SloBloLabs/LivSynth/App/System/Clock.cpp

#include "Clock.h"
#include "main.h"
#include "Groove.h"
#include <cmath>
#include "MidiMessage.h"
#include "swvPrint.h"
#include "System.h"

Clock::Clock(ClockTimer &timer) :
    _timer(timer)
{
    resetTicks();
    _ppqn = CONFIG_PPQN;
    _masterBpm = 120.f;
    _runState = RunState::Idle;
    _slaveDivisor = CONFIG_PPQN / 24; // -> 8
    _timer.attach(this);
}

void Clock::init() {
    _timer.disable();
}

void Clock::masterStart() {
    setRunState(RunState::MasterRunning);
    resetTicks();

    _timer.disable();
    setupMasterTimer();
    _timer.enable();
}

void Clock::masterStop() {
    setRunState(RunState::Idle);
    _timer.disable();
}

void Clock::resetTicks() {
    _tick = 0;
    _tickProcessed = 0;
    _slaveSubTicksPending = 0;
    _output.nextTick = 0;
}

void Clock::setMasterBpm(float bpm) {
    _masterBpm = bpm;
    if(_runState == RunState::MasterRunning) {
        setupMasterTimer();
    }
}

// called with each MIDI RT Clock event (0xF8)
void Clock::slaveTick() {

    // there are 24 midi clocks per quarter note
    // 12 clocks are a 8th note
    // 6 clocks are a 16th note
    // 120 bpm = 120 quarter notes per minute -> 1 clock every 20833,33 microseconds
    // == 60000000 microseconds per minute / (24 * 120 beats)

    if(_runState != RunState::SlaveRunning) return;

    // protect against clock rate overload
    _slaveSubTicksPending = std::min(_slaveSubTicksPending + _slaveDivisor, 2 * _slaveDivisor);
    
    // time elapsed since last tick
    uint32_t periodUs = _elapsedUs - _lastSlaveTickUs;

    _lastSlaveTickUs = _elapsedUs;

    // default tick period to 120 bpm
    if(_slaveTickPeriodUs == 0) {
        _slaveTickPeriodUs = (60 * 1000000 * _slaveDivisor) / (120 * _ppqn);
    }

    // update tick period if we have a valid measurement
    if(periodUs > 0 && _lastSlaveTickUs > 0) {
        _slaveTickPeriodUs = periodUs;
    }

    _slaveSubTickPeriodUs = _slaveTickPeriodUs / _slaveSubTicksPending;
    if(_elapsedUs - _nextSlaveSubTickUs > 1000) {
        _nextSlaveSubTickUs = _elapsedUs;
    } else {
        _nextSlaveSubTickUs += _slaveSubTickPeriodUs;
    }

    // estimate slave bpm
    if(periodUs > 0 && _lastSlaveTickUs > 0) {
        float bpm = (60.f * 1000000 * _slaveDivisor) / (periodUs * _ppqn);
        _slaveBpmFiltered = .9f * _slaveBpmFiltered + .1f * bpm;
        _slaveBpmAvg.push(_slaveBpmFiltered);
        _slaveBpm = _slaveBpmAvg();
        
        //ITM_SendChar(bpm, 1);
        //ITM_SendChar(_slaveBpmFiltered, 2);
        //ITM_SendChar(_slaveBpm, 3);
        //UDBG("E:%ld, L:%ld, B:%.2f, S: %.2f\n", _elapsedUs, _lastSlaveTickUs, bpm, _slaveBpm);
    }
}

void Clock::slaveStart() {
    if(_runState == RunState::MasterRunning) {
        return;
    }

    setRunState(RunState::SlaveRunning);

    resetTicks();

    _timer.disable();
    setupSlaveTimer();

    for(auto observer : _observerList) {
        observer->onStart();
    }

    _timer.enable();
}

void Clock::slaveStop() {
    if(_runState != RunState::SlaveRunning) {
        return;
    }

    for(auto observer : _observerList) {
        observer->onStop();
    }

    masterStop();
}

void Clock::slaveContinue() {
    if(_runState != RunState::Idle) {
        return;
    }

    setRunState(RunState::SlaveRunning);

    setupSlaveTimer();
    _timer.enable();
}

void Clock::slaveReset() {
    if(_runState == RunState::MasterRunning) {
        return;
    }

    setRunState(RunState::Idle);

    _timer.disable();
}

// called by USB ISR
void Clock::slaveHandleMidi(uint8_t msg) {
    switch (MidiMessage::realTimeMessage(msg)) {
    case MidiMessage::Tick:
        slaveTick();
        break;
    case MidiMessage::Start:
        slaveStart();
        break;
    case MidiMessage::Stop:
        slaveStop();
        break;
    case MidiMessage::Continue:
        slaveContinue();
        break;
    default:
        break;
    }
}

// outputDivisor * (_clock.ppqn() / SEQUENCE_PPQN), outputPulse
// outputDivisor = 12 -> 1/16 note
// ppqn = 192
// SEQUENCE_PPQN = 48
// divisor = 12 * (192 / 48) = 12 * 4 = 48
// outputPulse = 1
/*
Divisor	Note	Name
2	1/64T	Triplet sixty-fourth note
3	1/64	Sixty-fourth note
4	1/32T	Triplet thirty-second note
6	1/32	Thirty-second note
8	1/16T	Triplet sixteenth note
9	1/32.	Dotted thirty-second note
12	1/16	Sixteenth note
16	1/8T	Triplet eighth note
18	1/16.	Dotted sixteenth note
24	1/8	    Eighth note
32	1/4T	Triplet quarter note
36	1/8.	Dotted eighth note
48	1/4	    Quarter note
64	1/2T	Triplet half note
72	1/4.	Dotted quarter note
96	1/2	    Half note
128	1T	    Triplet whole note
144	1/2.	Dotted half note
192	1	    Whole note
256	2T	    Triplet double note
288	1.	    Dotted whole note
384	2	    Double note
512	4T	    Triplet quadruple note
576	2.	    Dotted double note
768	4	    Quadruple note
 -> see Model/KnownDivisor.h
*/
void Clock::outputConfigure(int divisor, int pulse) {
    _output.divisor = divisor;
    _output.pulse = pulse;
}

void Clock::outputConfigureSwing(int swing) {
    _output.swing = swing;
}

bool Clock::checkTick(uint32_t* tick) {
    if(_tickProcessed < _tick) {
        *tick = _tickProcessed++;
        return true;
    }
    return false;
}

 // called from ClockTimer ISR
void Clock::onClockTimerTick() {
    //DBG("Clock Timer Tick");
    switch(_runState) {
    case RunState::MasterRunning: {
        outputTick(_tick);
        ++_tick;
        _elapsedUs += _timer.period();
        break;
    }
    case RunState::SlaveRunning: {
        _elapsedUs += _timer.period();

        if(_slaveSubTicksPending > 0 && _elapsedUs >= _nextSlaveSubTickUs) {
            // process DIO pulse
            outputTick(_tick);
            ++_tick;
            --_slaveSubTicksPending;
            _nextSlaveSubTickUs += _slaveSubTickPeriodUs;
        }

        if((_elapsedUs - _lastSlaveTickUs) > 500000) {
            //UDBG("Auto Slave Reset\n");
            slaveReset();
        }

        //ITM_SendChar(_elapsedUs, 4);
        //ITM_SendChar(_slaveSubTicksPending, 5);
        //ITM_SendChar(_nextSlaveSubTickUs, 6);
        //ITM_SendChar(_tick, 7);
        break;
    }
    default:
        break;
    }
}

void Clock::setupMasterTimer() {
    _elapsedUs = 0;
    // round() reduces errors in period calculation, especially for bpm > 120 where only 1 us can determine the tempo on the tenths place.
    // From 181 onwards the difference in period can be zero from one tenth bpm to the next.
    // This is 8 times fast than midi clock.
    uint32_t us = std::round((60 * 1000000) / (_masterBpm * _ppqn));
    _timer.setPeriod(us);
}

void Clock::setupSlaveTimer() {
    _elapsedUs = 0;
    _lastSlaveTickUs = 0;

    _timer.setPeriod(SlaveTimerPeriod); // 100 -> 3125 bpm ?
}

// called from onClockTimerTick
void Clock::outputTick(uint32_t tick) {

    auto applySwing = [this] (uint32_t tick) {
        if(_output.swing != 0) {
            return Groove::applySwing(tick, _output.swing);
        }
        return tick;
    };

    if(tick == _output.nextTick) {
        uint32_t divisor = _output.divisor;
        // "at least 1 tick long (e.g. 2,604ms @ 120 bpm), the second term kicks in at bpm > 312,5 if pulse equals 1"
        uint32_t clockDuration = std::max(uint32_t(1), uint32_t(_masterBpm * _ppqn * _output.pulse / (60 * 1000)));

        _output.nextTickOn = applySwing(_output.nextTick);
        _output.nextTickOff = std::min(_output.nextTickOn + clockDuration, applySwing(_output.nextTick + divisor) - 1);
        
        _output.nextTick += divisor;
    }

    // handle DIO output
    if(tick == _output.nextTickOn) {
        outputClock(true);
    }

    if(tick == _output.nextTickOff) {
        outputClock(false);
    }
}

// DIO output
void Clock::outputClock(bool clock) {
    if(clock != _outputState.clock) {
        _outputState.clock = clock;
        // create reset trigger on 8th clock pulse
        _outputState.reset = !(_tick % (48 * 8));
        notifyObservers();
    }
}
