SloBloLabs/LivSynth/App/Config.h

#pragma once

// Parts per quarter note
#define CONFIG_PPQN            192

// Sequence parts per quarter note resolution
#define CONFIG_SEQUENCE_PPQN    48

// Model
#define CONFIG_PATTERN_COUNT     8

// Buttons
#define CONFIG_NUM_BUTTONS      16

// Pots
#define CONFIG_NUM_POTS          2
